msticninja/ProForge-4.2/Config Files/mainsail.cfg

## Client klipper macro definitions
##
## Copyright (C) 2022 Alex Zellner <alexander.zellner@googlemail.com>
##
## This file may be distributed under the terms of the GNU GPLv3 license
##
## !!! This file is read-only. Maybe the used editor indicates that. !!!
##
## Customization:
##   1) copy the gcode_macro _CLIENT_VARIABLE (see below) to your printer.cfg
##   2) remove the comment mark (#) from all lines
##   3) change any value in there to your needs
##
## Use the PAUSE macro direct in your M600:
##  e.g. with a different park position front left and a minimal height of 50 
##    [gcode_macro M600]
##    description: Filament change
##    gcode: PAUSE X=10 Y=10 Z_MIN=50
##  Z_MIN will park the toolhead at a minimum of 50 mm above to bed to make it easier for you to swap filament.
##
## Client variable macro for your printer.cfg
#[gcode_macro _CLIENT_VARIABLE]
## !!! Caution [firmware_retraction] must be defined in the printer.cfg if you set use_fw_retract: True !!!
#variable_use_fw_retract   : False ; use fw_retraction instead of the manual version [True/False]
#variable_idle_timeout     : 0     ; time in sec until idle_timeout kicks in. Value 0 means that no value will be set or restored
#variable_runout_sensor    : ""    ; If a sensor is defined, it will be used to cancel the execution of RESUME in case no filament is detected.
##                                   Specify the config name of the runout sensor e.g "filament_switch_sensor runout". Hint use the same as in your printer.cfg
## !!! Custom macros, please use with care and review the section of the corresponding macro.
## These macros are for simple operations like setting a status LED. Please make sure your macro does not interfere with the basic macro functions.
## Only  single line commands are supported, please create a macro if you need more than one command.
#variable_user_pause_macro : ""    ; Everything inside the "" will be executed after the klipper base pause (PAUSE_BASE) function
#variable_user_resume_macro: ""    ; Everything inside the "" will be executed before the klipper base resume (RESUME_BASE) function
#variable_user_cancel_macro: ""    ; Everything inside the "" will be executed before the klipper base cancel (CANCEL_PRINT_BASE) function
#gcode:

[virtual_sdcard]
path: ~/printer_data/gcodes
on_error_gcode: CANCEL_PRINT

[pause_resume]
#recover_velocity: 50.
#   When capture/restore is enabled, the speed at which to return to
#   the captured position (in mm/s). Default is 50.0 mm/s.

[display_status]

[respond]
  
[gcode_macro _CLIENT_EXTRUDE]
description: Extrudes, if the extruder is hot enough
gcode:
  ##### get user parameters or use default #####
  {% set client = printer['gcode_macro _CLIENT_VARIABLE']|default({}) %}
  {% set use_fw_retract = (client.use_fw_retract|default(false)|lower == 'true') and (printer.firmware_retraction is defined) %}
  {% set length = params.LENGTH|default(client.unretract)|default(1.0)|float %}
  {% set speed = params.SPEED|default(client.speed_unretract)|default(35) %}
  {% set absolute_extrude = printer.gcode_move.absolute_extrude %}
  ##### end of definitions #####
  {% if printer.toolhead.extruder != '' %}
    {% if printer[printer.toolhead.extruder].can_extrude %}
      {% if use_fw_retract %}
        {% if length < 0 %}
          G10
        {% else %}
          G11
        {% endif %}
      {% else %}
        M83
        G1 E{length} F{(speed|float|abs) * 60}
        {% if absolute_extrude %}
          M82
        {% endif %}
      {% endif %}
    {% else %}
      RESPOND TYPE=echo MSG='{"\"%s\" not hot enough" % printer.toolhead.extruder}'
    {% endif %}
  {% endif %}

[gcode_macro _CLIENT_RETRACT]
description: Retracts, if the extruder is hot enough
gcode:
  {% set client = printer['gcode_macro _CLIENT_VARIABLE']|default({}) %}
  {% set length = params.LENGTH|default(client.retract)|default(1.0)|float %}
  {% set speed = params.SPEED|default(client.speed_retract)|default(35) %}

  _CLIENT_EXTRUDE LENGTH=-{length|float|abs} SPEED={speed|float|abs}

[gcode_macro _CLIENT_LINEAR_MOVE]
description: Linear move with save and restore of the gcode state
gcode:
  {% set x_move = "X" ~ params.X if params.X is defined else "" %}
  {% set y_move = "Y" ~ params.Y if params.Y is defined else "" %}
  {% set z_move = "Z" ~ params.Z if params.Z is defined else "" %}
  {% set e_move = "E" ~ params.E if params.E is defined else "" %}
  {% set rate = "F" ~ params.F if params.F is defined else "" %}
  {% set ABSOLUTE = params.ABSOLUTE | default(0) | int != 0 %}
  {% set ABSOLUTE_E = params.ABSOLUTE_E | default(0) | int != 0 %}
  SAVE_GCODE_STATE NAME=_client_movement
  {% if x_move or y_move or z_move %}
    G9{ 0 if ABSOLUTE else 1 }
  {% endif %}
  {% if e_move %}
    M8{ 2 if ABSOLUTE_E else 3 }
  {% endif %}
  G1 { x_move } { y_move } { z_move } { e_move } { rate }
  RESTORE_GCODE_STATE NAME=_client_movement
